shchuko/MeteoBox/images/2.jpg

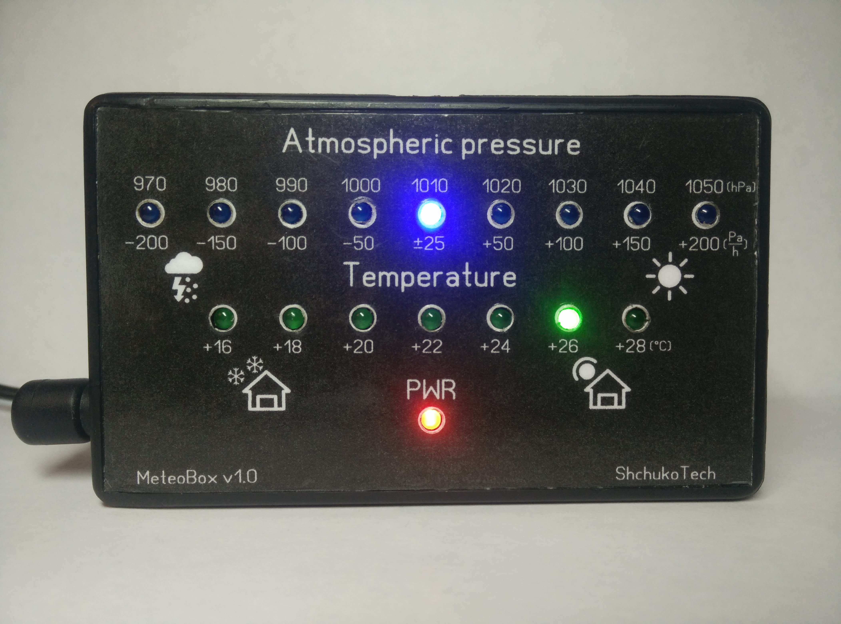
images/2.jpg
