shchuko/MeteoBox/images/5.jpg

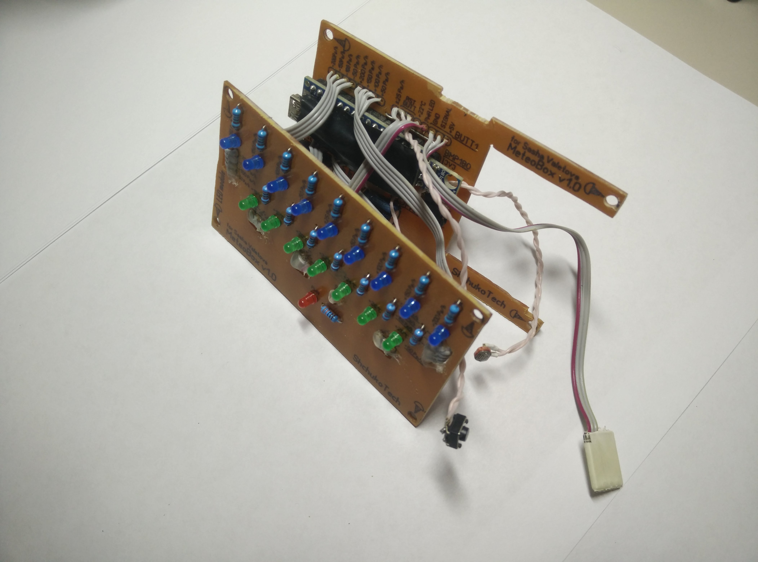
images/5.jpg
